rsjpark/A_Keyboard_For_Me/slide images/0.1_kle_to_matrix_converter.png

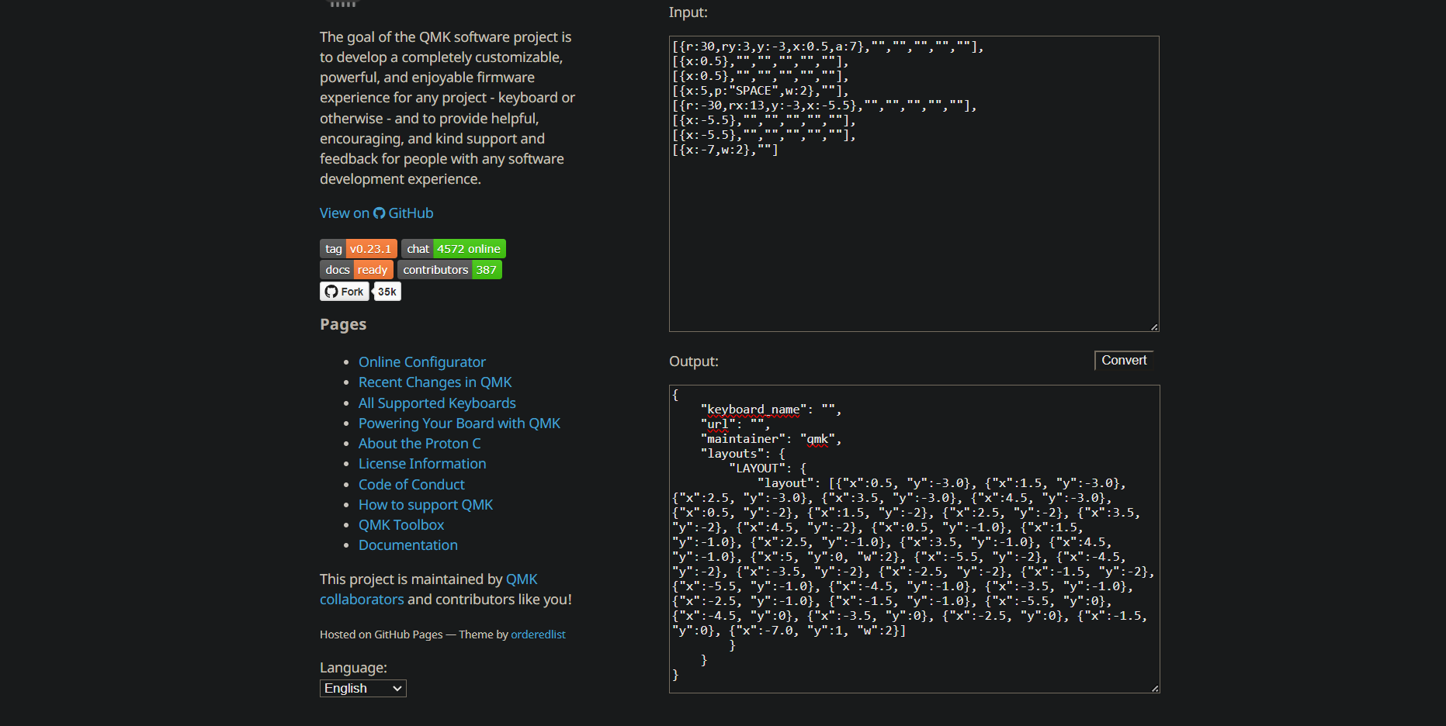
slide images/0.1_kle_to_matrix_converter.png
