rsjpark/A_Keyboard_For_Me/slide images/0.4_firmware_compile_trick.png

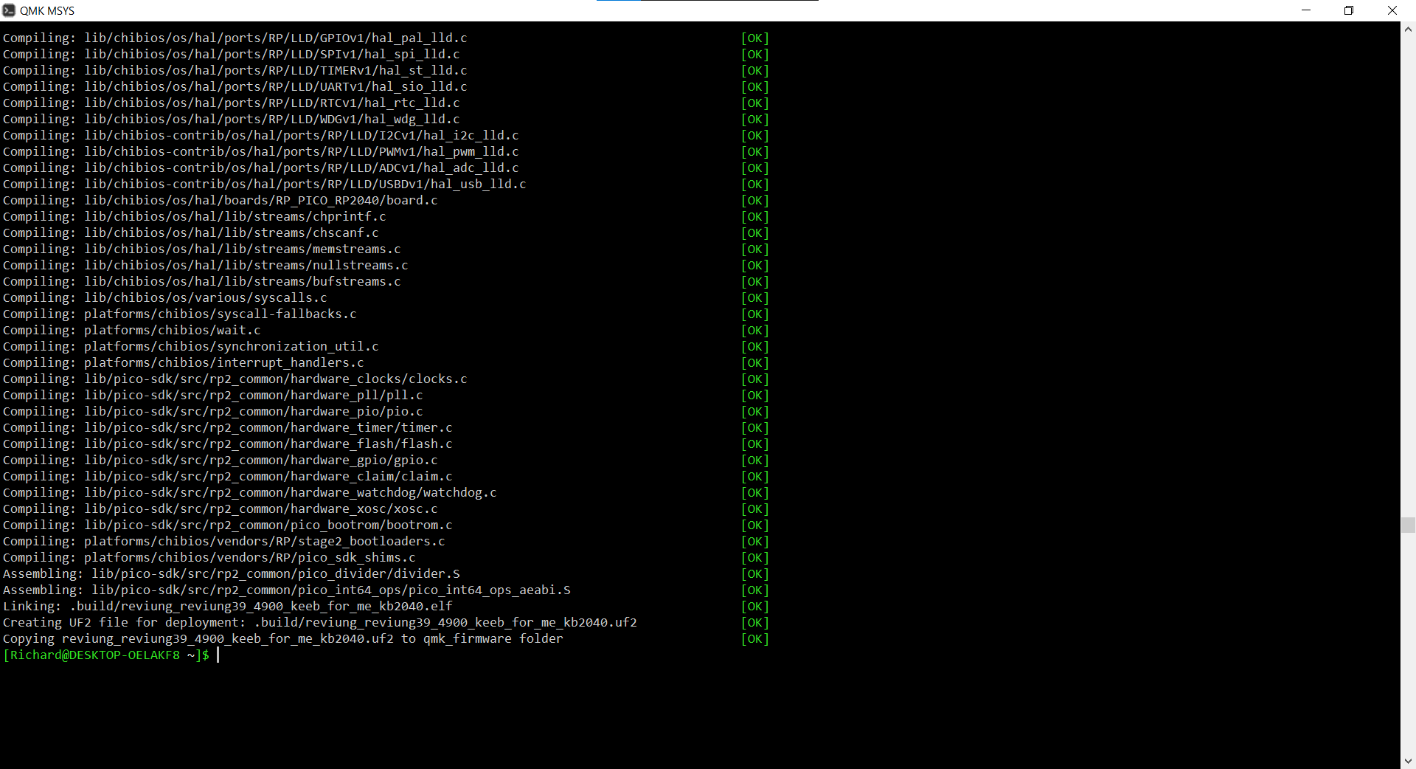
slide images/0.4_firmware_compile_trick.png
