rsjpark/A_Keyboard_For_Me/slide images/001.jpg

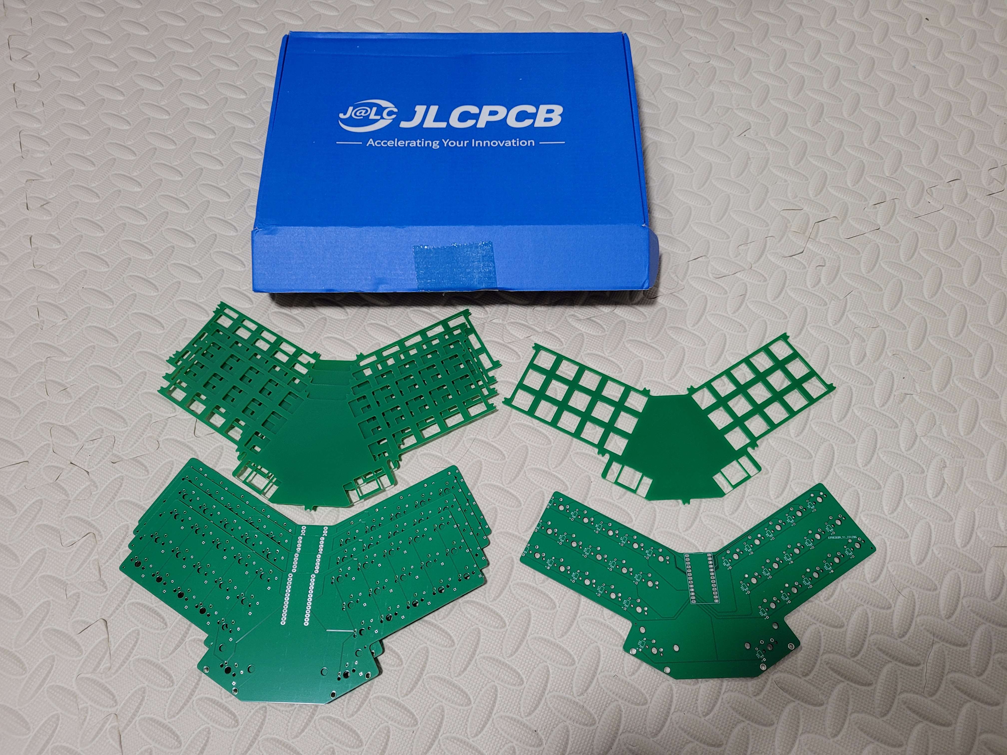
slide images/001.jpg
