rsjpark/A_Keyboard_For_Me/slide images/002.jpg

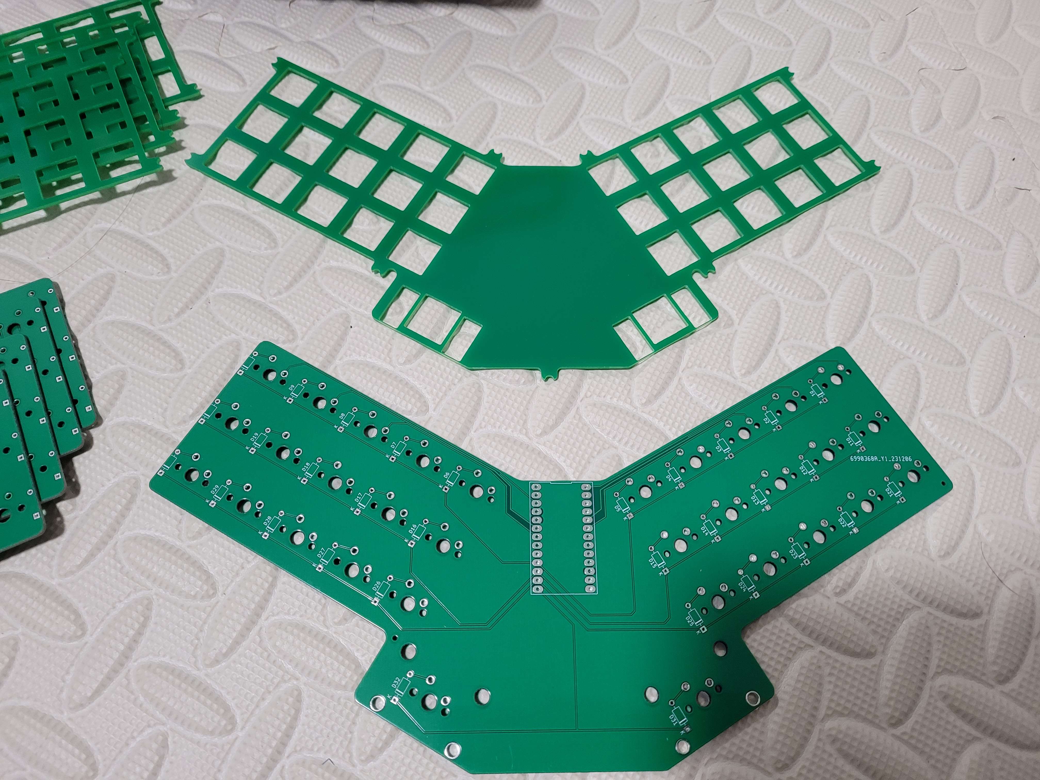
slide images/002.jpg
