rsjpark/A_Keyboard_For_Me/slide images/003.jpg

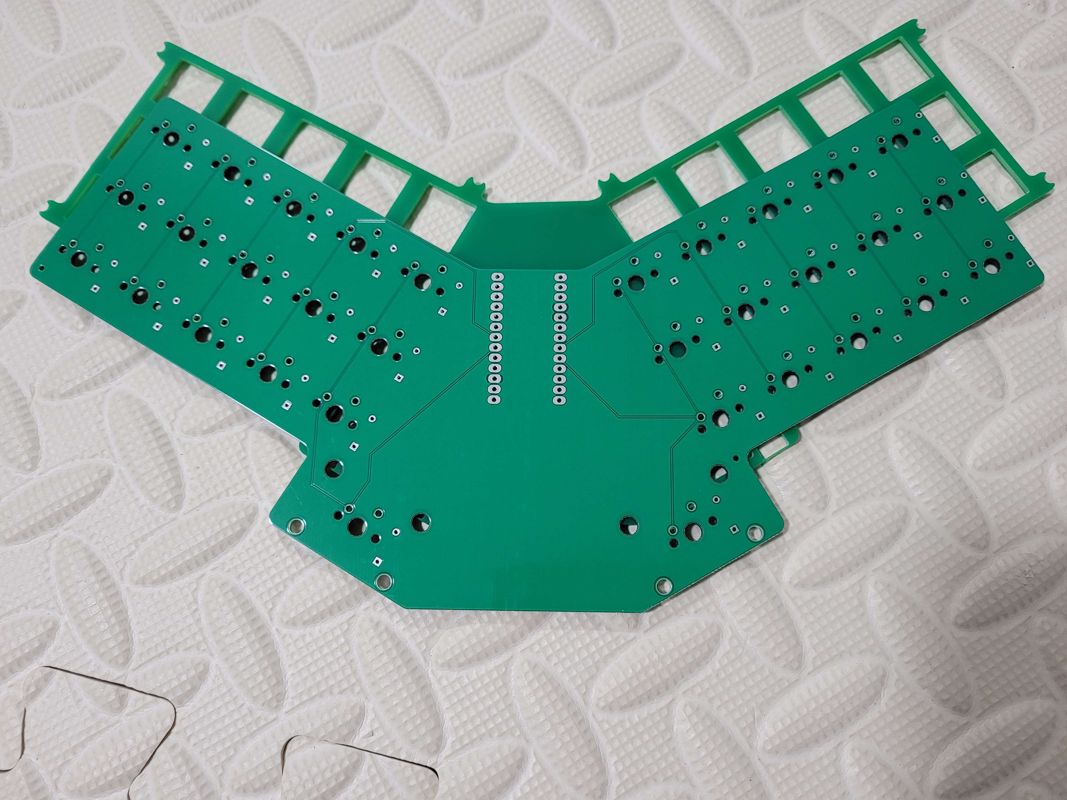
slide images/003.jpg
