rsjpark/A_Keyboard_For_Me/slide images/004.jpg

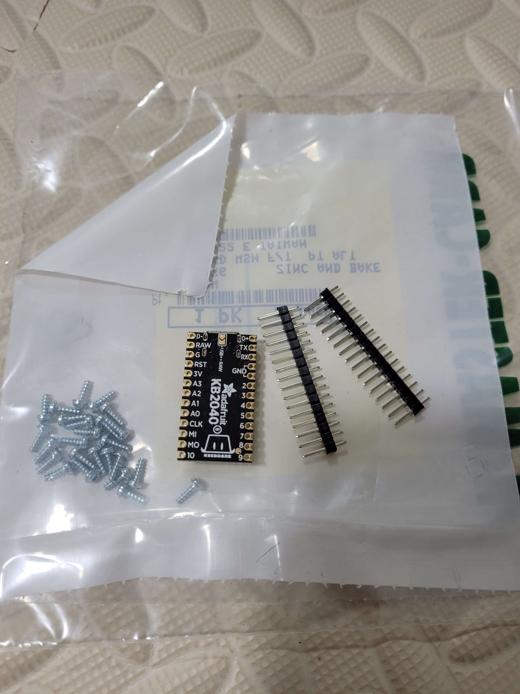
slide images/004.jpg
