rsjpark/A_Keyboard_For_Me/slide images/005.jpg

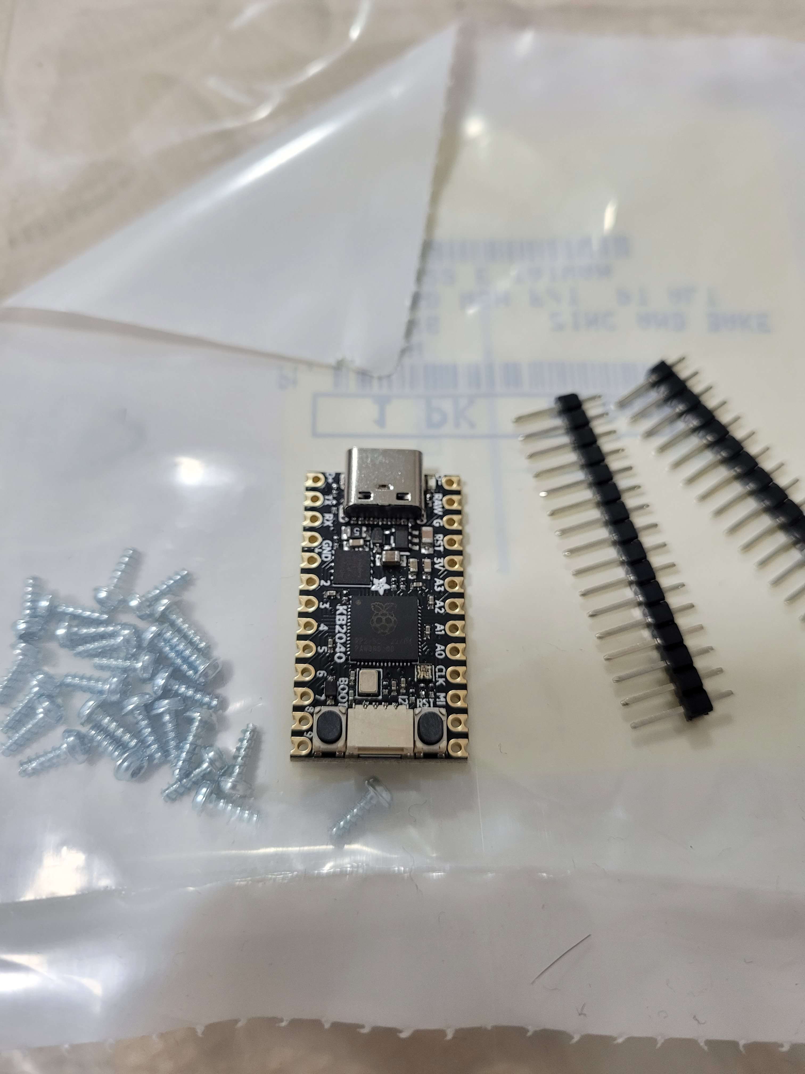
slide images/005.jpg
