rsjpark/A_Keyboard_For_Me/slide images/006.jpg

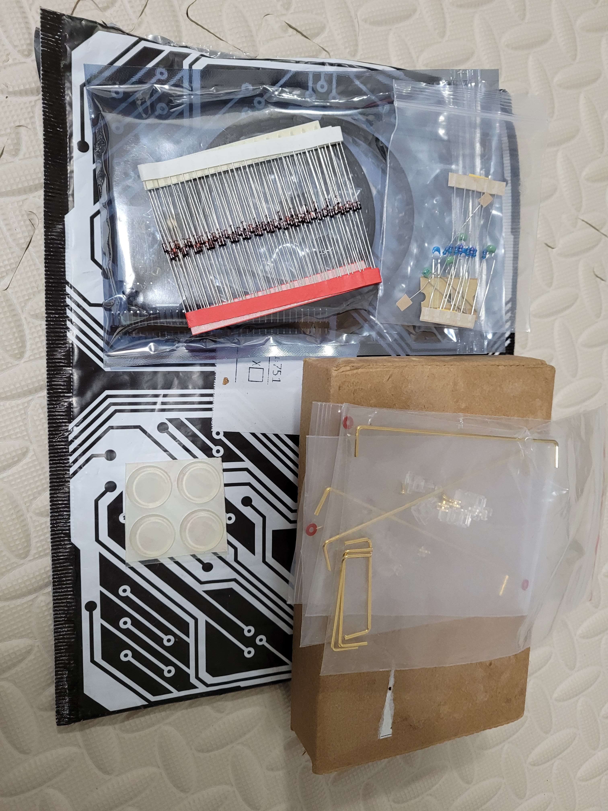
slide images/006.jpg
