rsjpark/A_Keyboard_For_Me/slide images/008.jpg

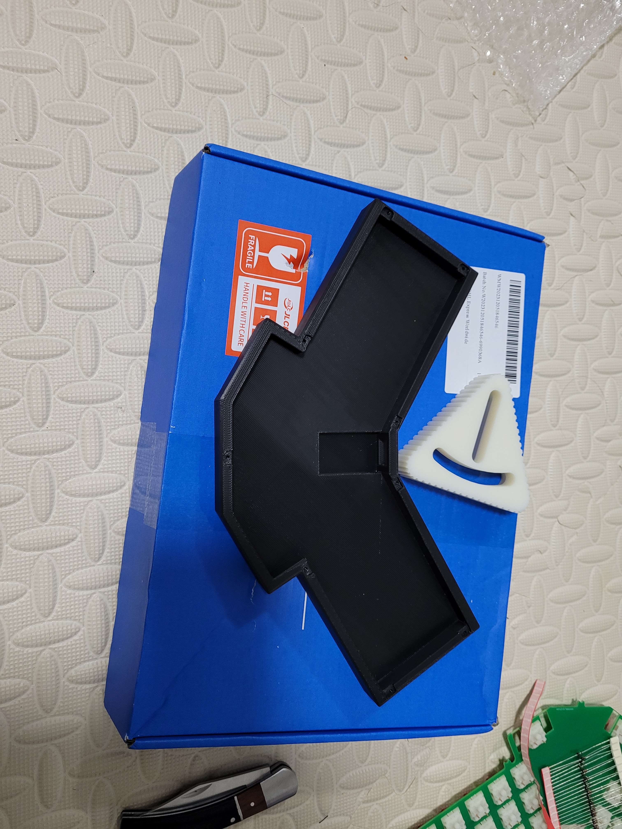
slide images/008.jpg
