rsjpark/A_Keyboard_For_Me/slide images/009.jpg

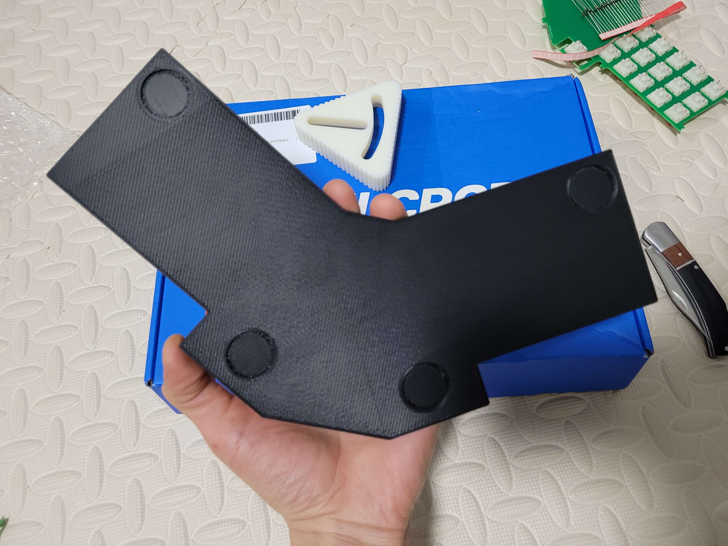
slide images/009.jpg
