rsjpark/A_Keyboard_For_Me/slide images/010.jpg

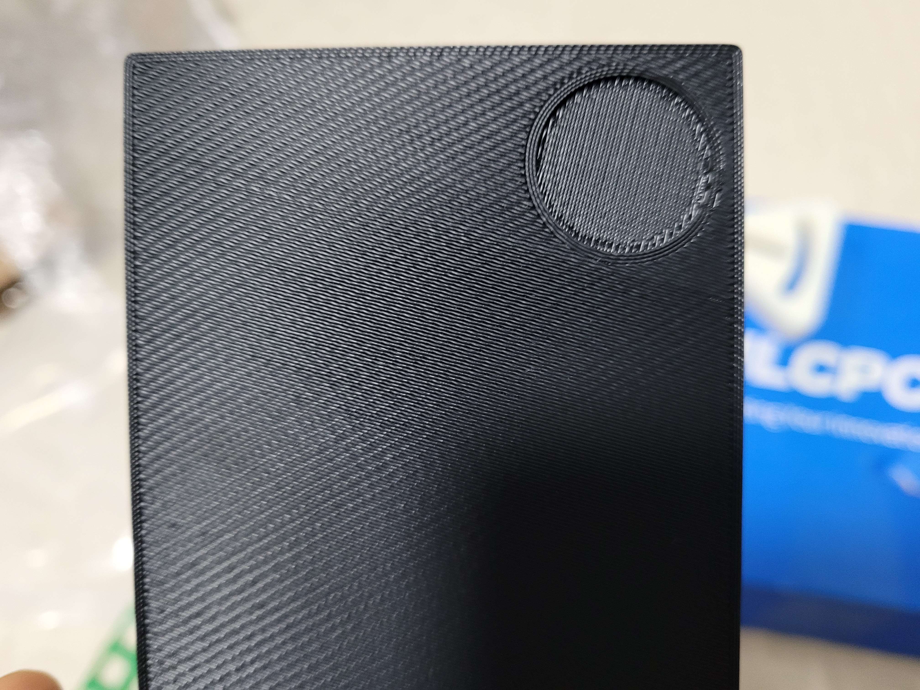
slide images/010.jpg
