rsjpark/A_Keyboard_For_Me/slide images/011.jpg

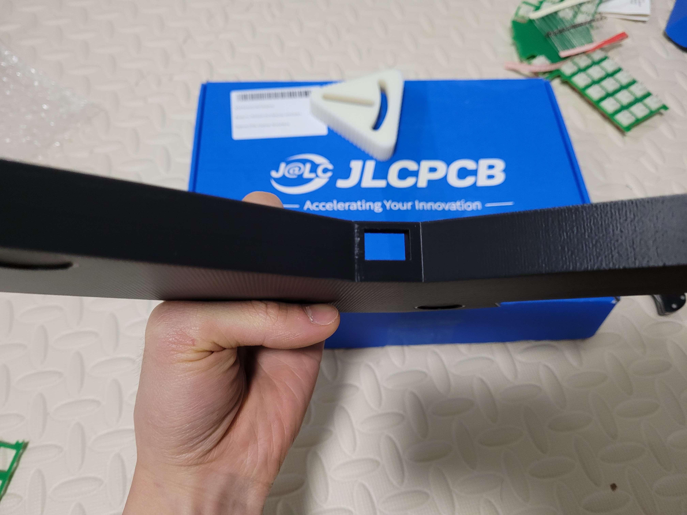
slide images/011.jpg
