rsjpark/A_Keyboard_For_Me/slide images/012.jpg

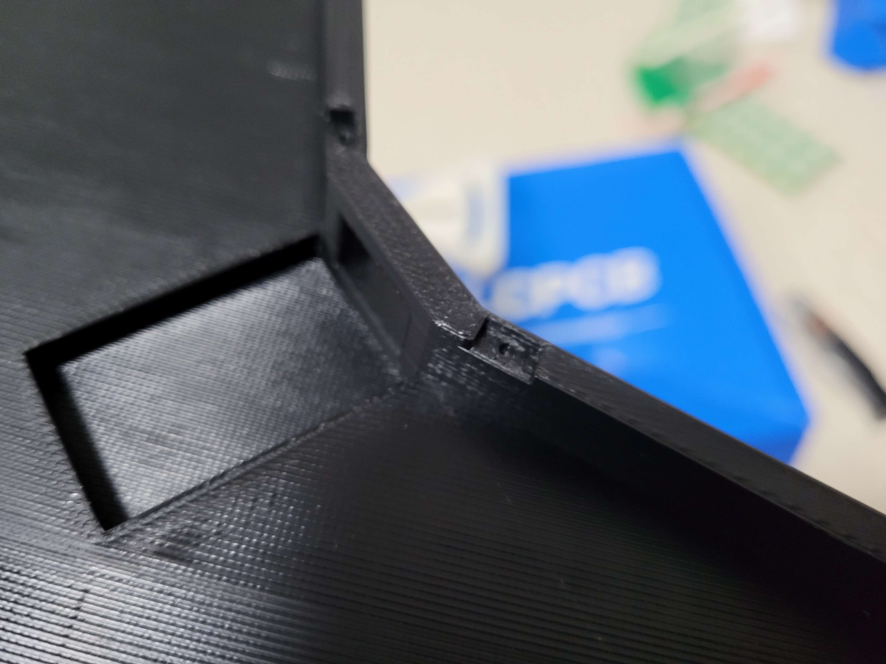
slide images/012.jpg
