rsjpark/A_Keyboard_For_Me/slide images/013.jpg

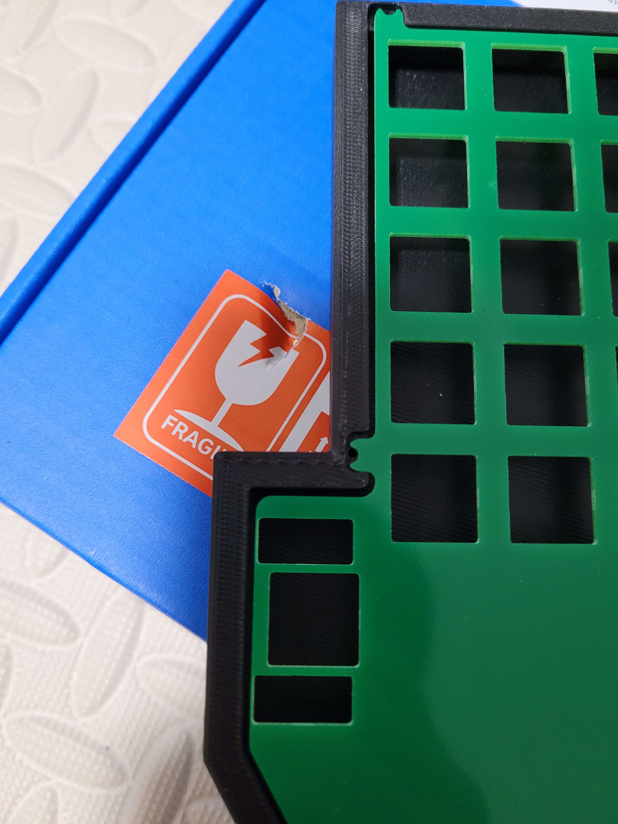
slide images/013.jpg
