rsjpark/A_Keyboard_For_Me/slide images/014.jpg

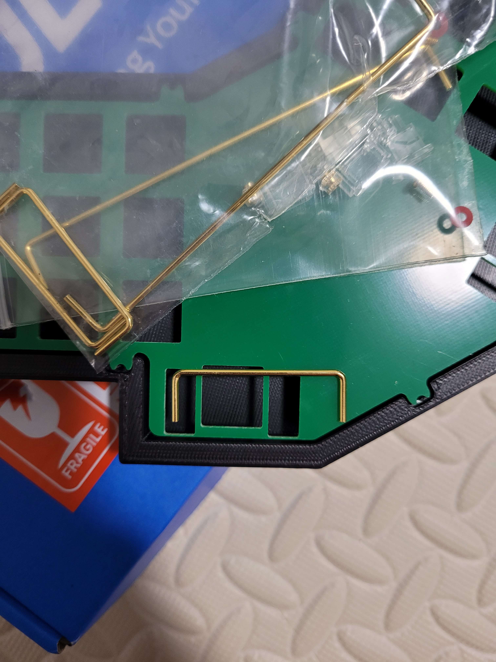
slide images/014.jpg
