rsjpark/A_Keyboard_For_Me/slide images/015.jpg

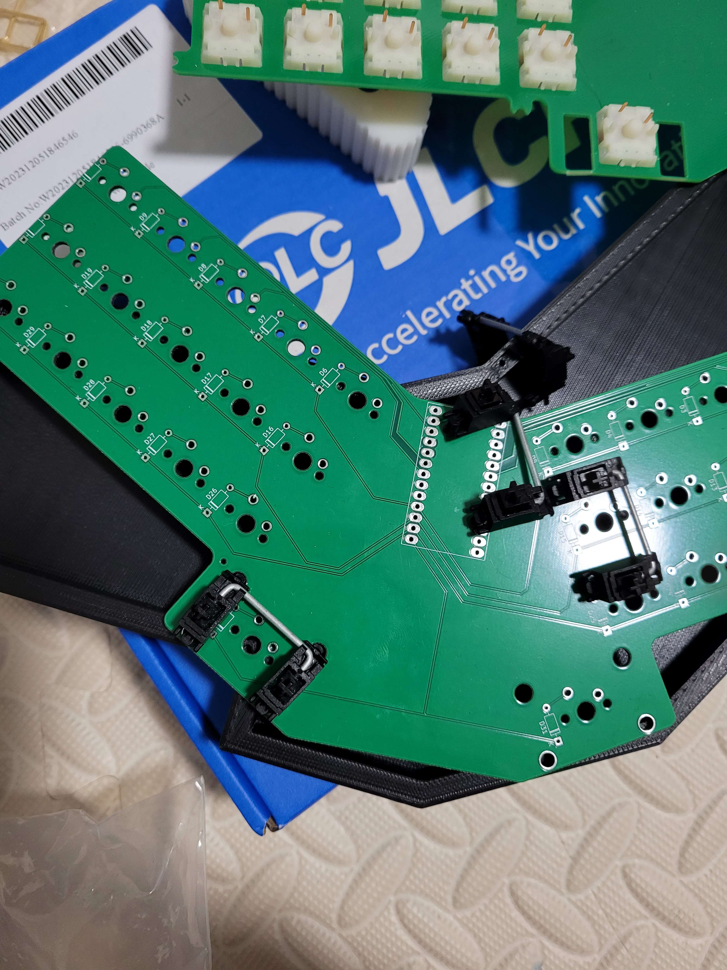
slide images/015.jpg
