rsjpark/A_Keyboard_For_Me/slide images/016.jpg

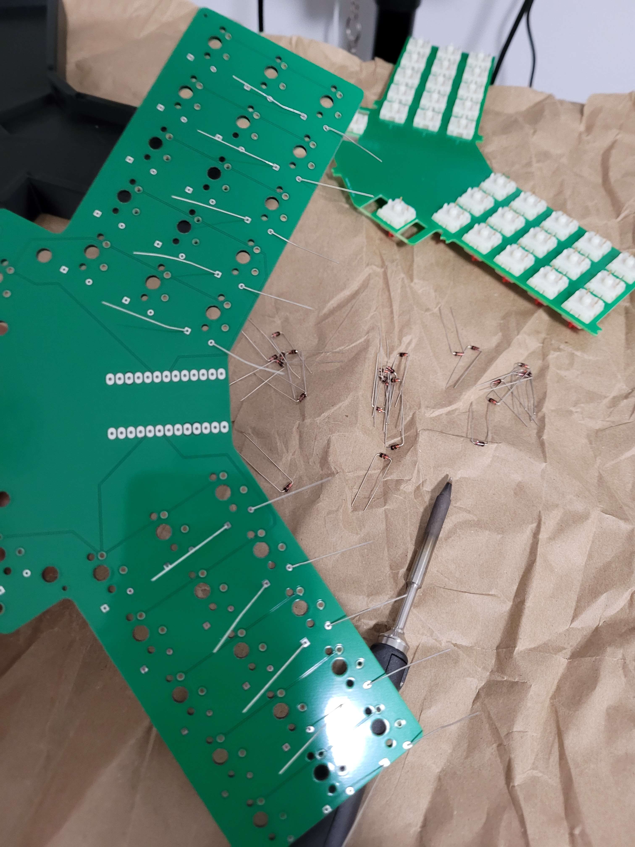
slide images/016.jpg
