rsjpark/A_Keyboard_For_Me/slide images/017.jpg

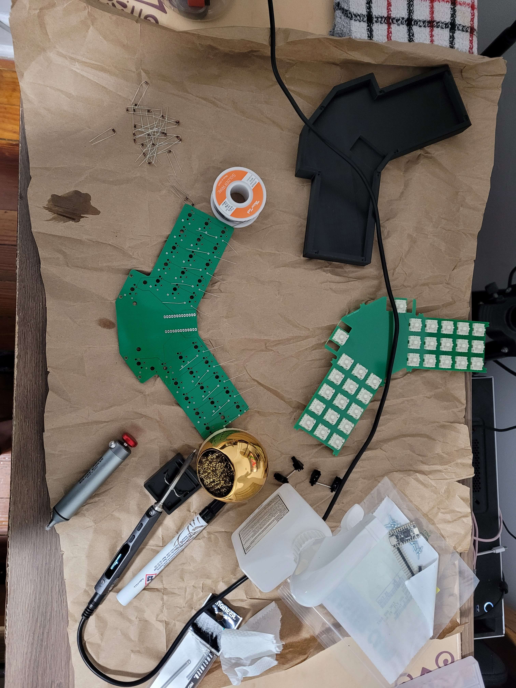
slide images/017.jpg
