rsjpark/A_Keyboard_For_Me/slide images/018.jpg

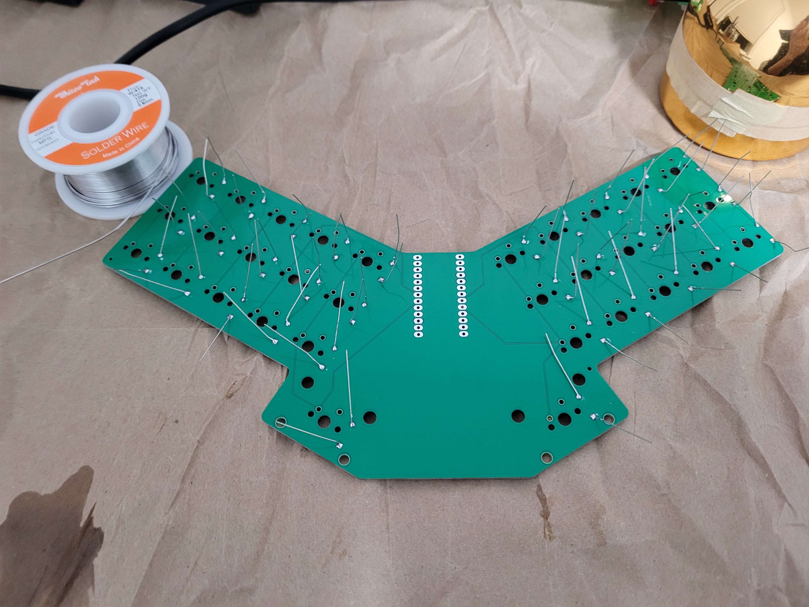
slide images/018.jpg
