rsjpark/A_Keyboard_For_Me/slide images/019.jpg

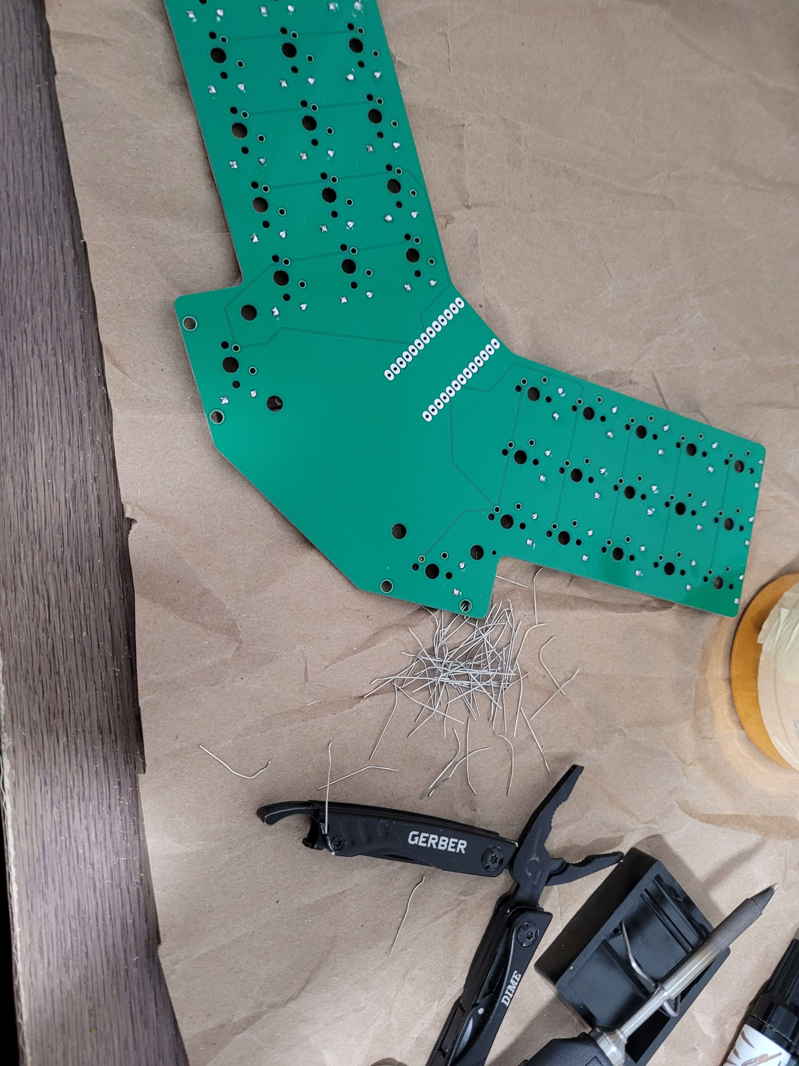
slide images/019.jpg
