rsjpark/A_Keyboard_For_Me/slide images/020.jpg

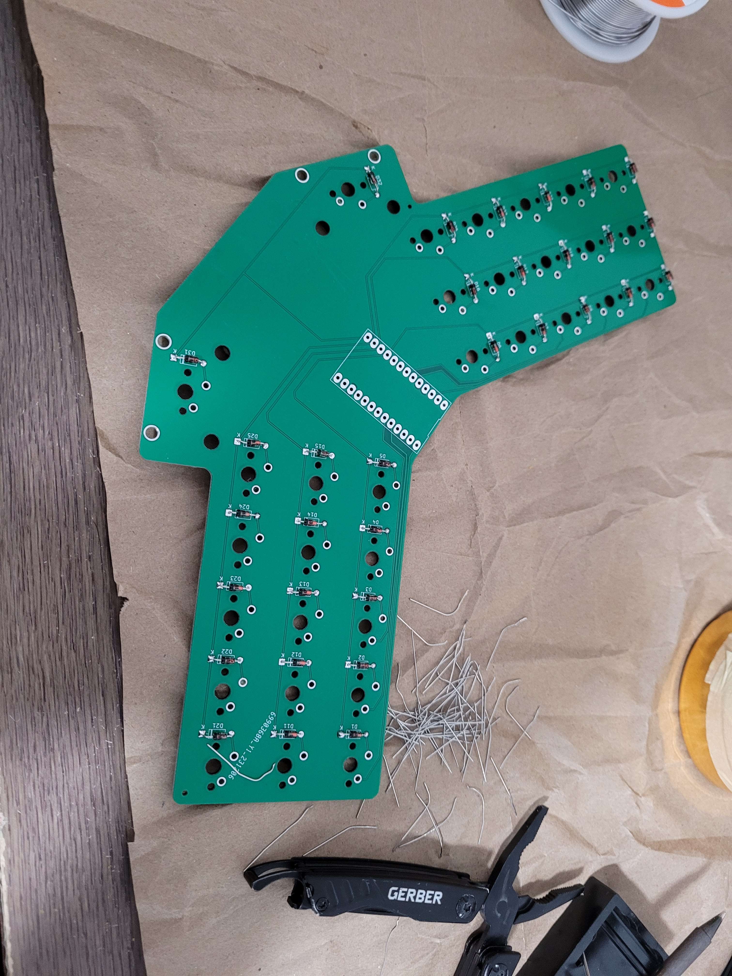
slide images/020.jpg
