rsjpark/A_Keyboard_For_Me/slide images/021.jpg

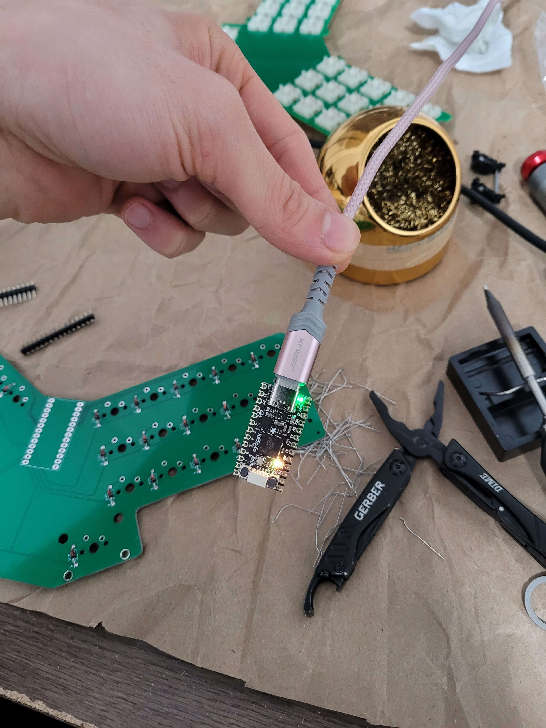
slide images/021.jpg
