rsjpark/A_Keyboard_For_Me/slide images/023.jpg

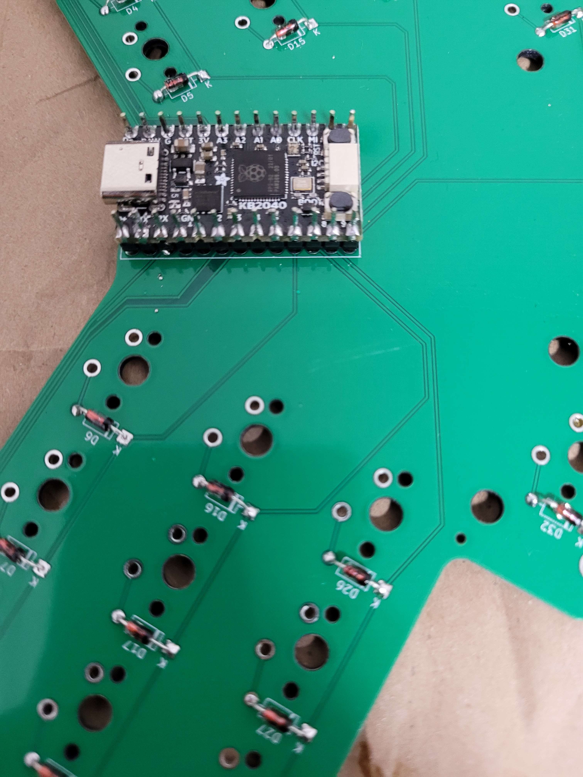
slide images/023.jpg
