rsjpark/A_Keyboard_For_Me/slide images/024.jpg

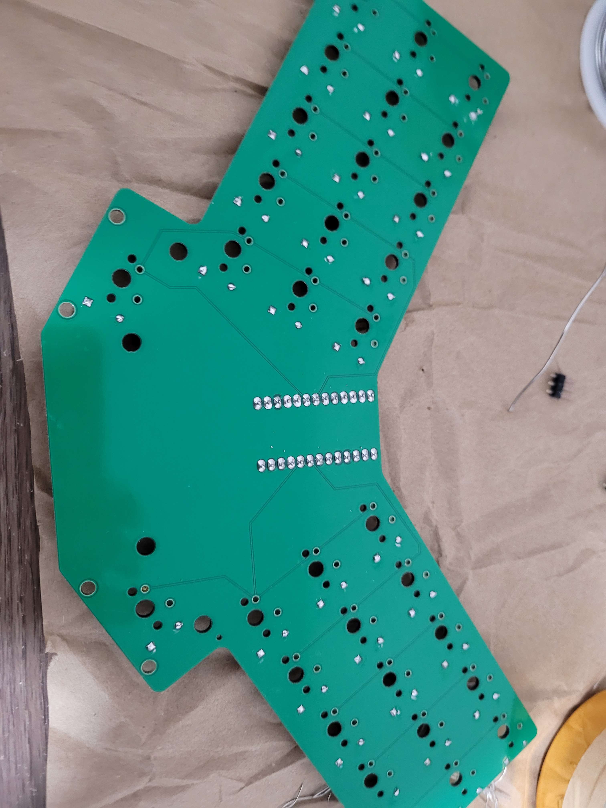
slide images/024.jpg
