rsjpark/A_Keyboard_For_Me/slide images/025.jpg

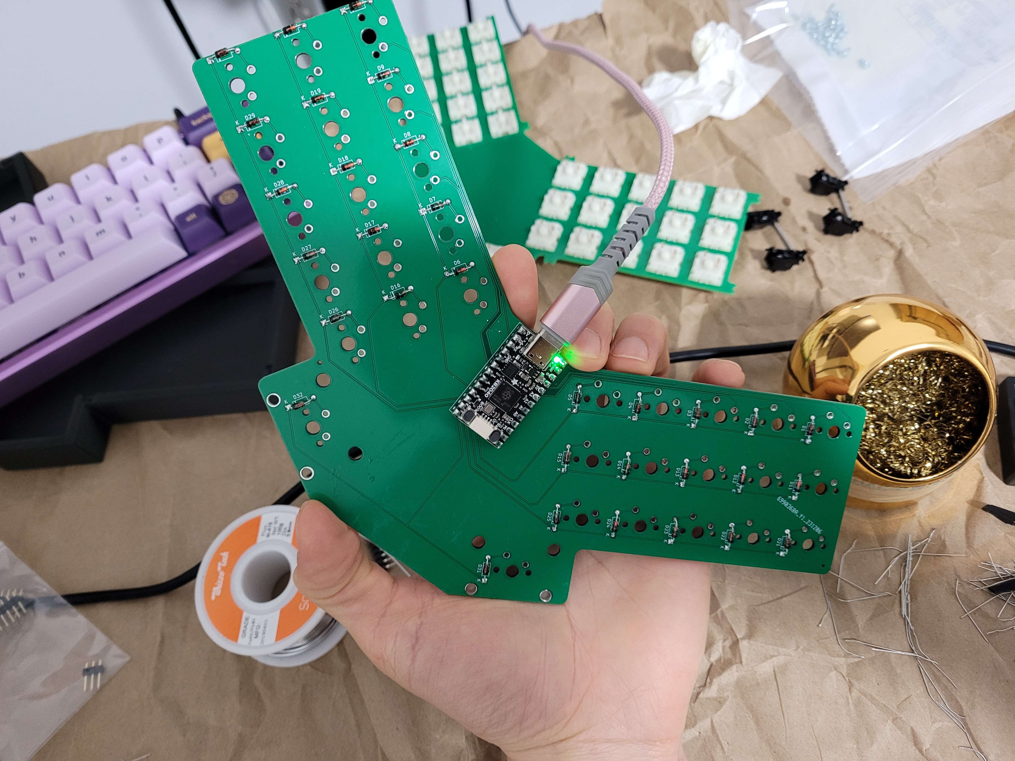
slide images/025.jpg
