rsjpark/A_Keyboard_For_Me/slide images/027.png

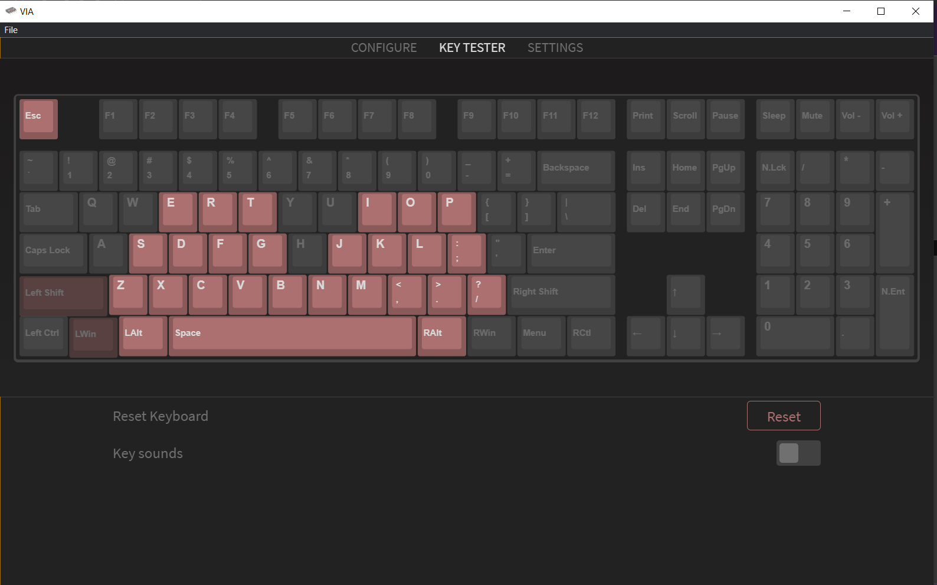
slide images/027.png
