rsjpark/A_Keyboard_For_Me/slide images/028.jpg

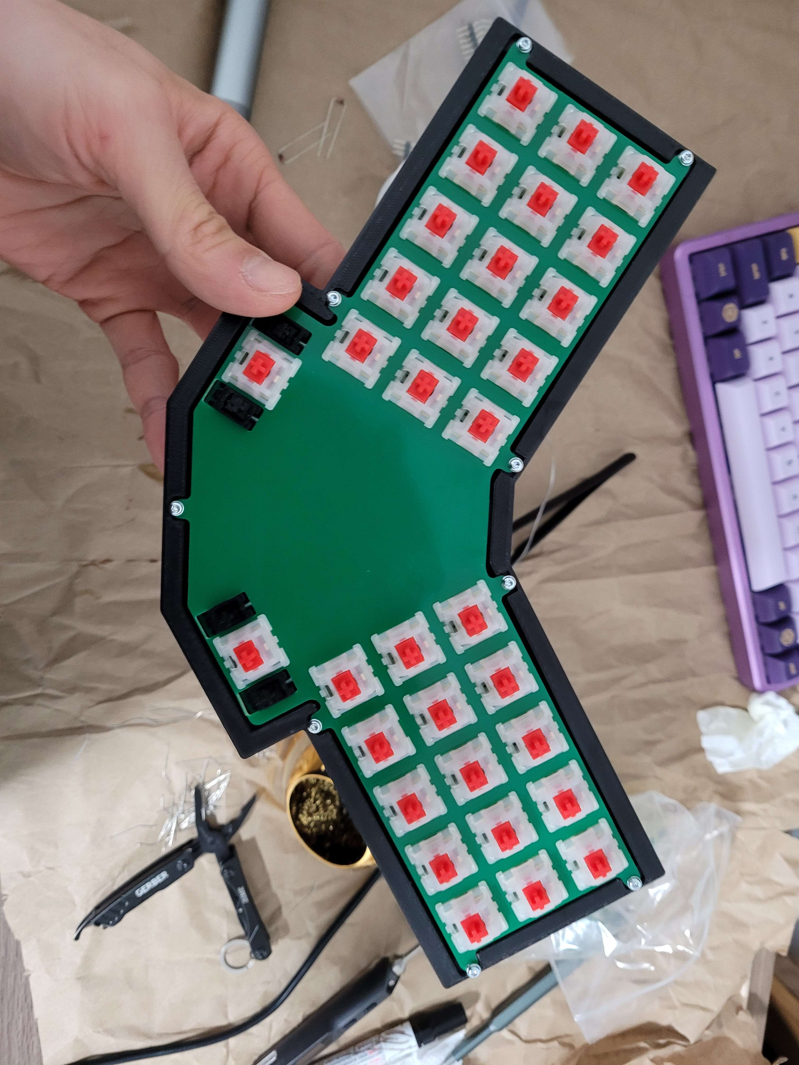
slide images/028.jpg
