rsjpark/A_Keyboard_For_Me/slide images/029.jpg

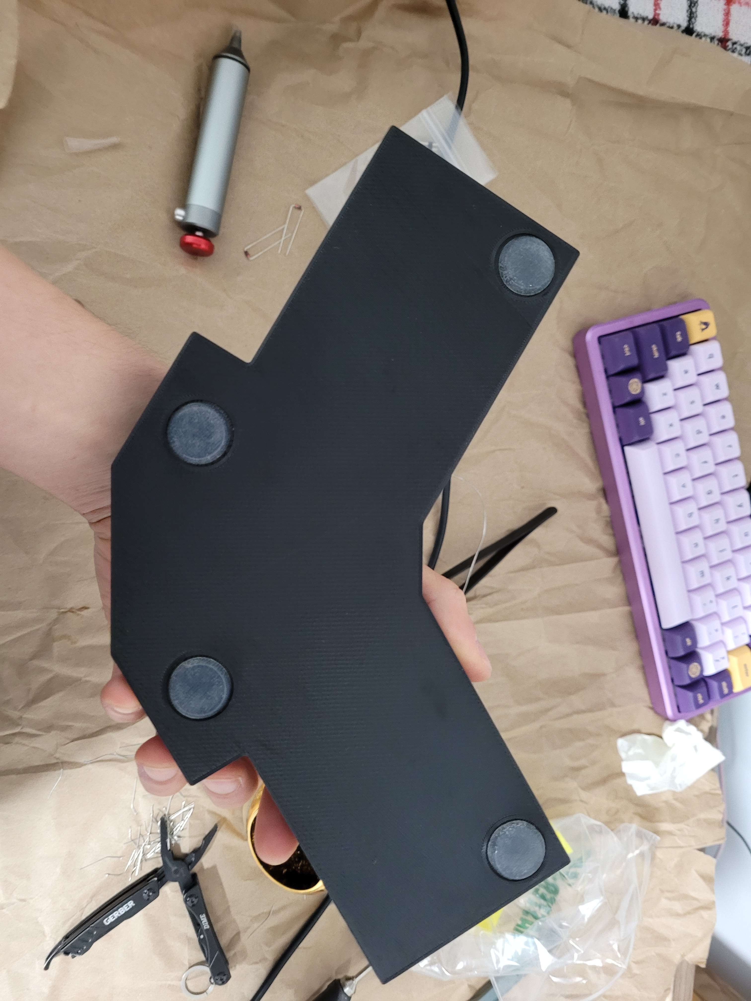
slide images/029.jpg
