rsjpark/A_Keyboard_For_Me/slide images/030.jpg

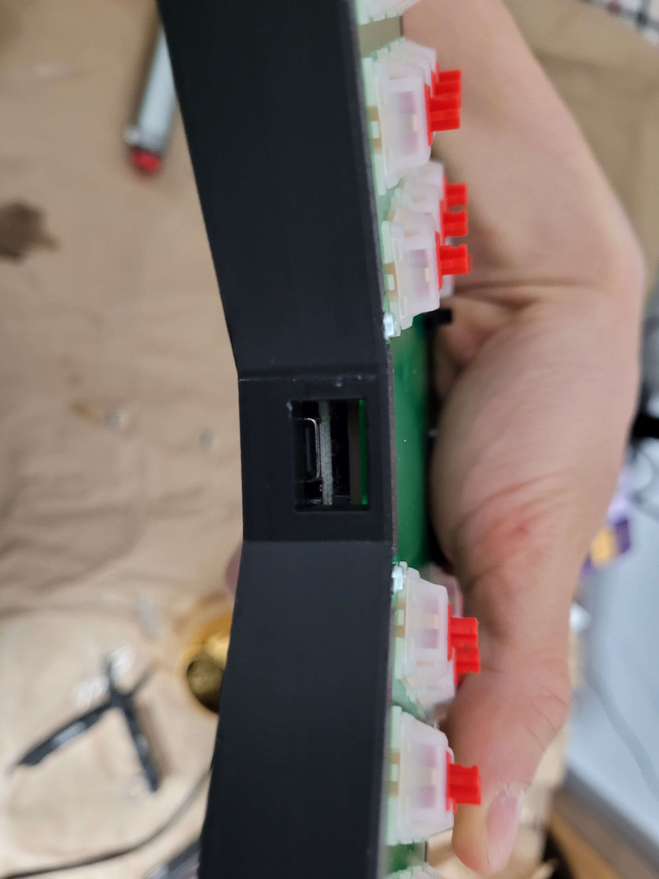
slide images/030.jpg
