rsjpark/A_Keyboard_For_Me/slide images/031.jpg

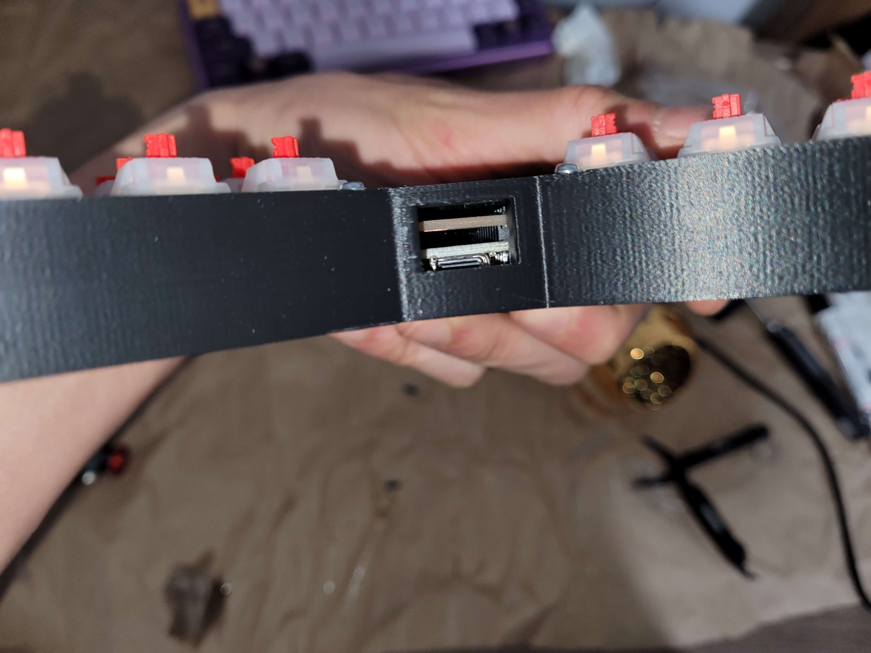
slide images/031.jpg
