rsjpark/A_Keyboard_For_Me/slide images/032.jpg

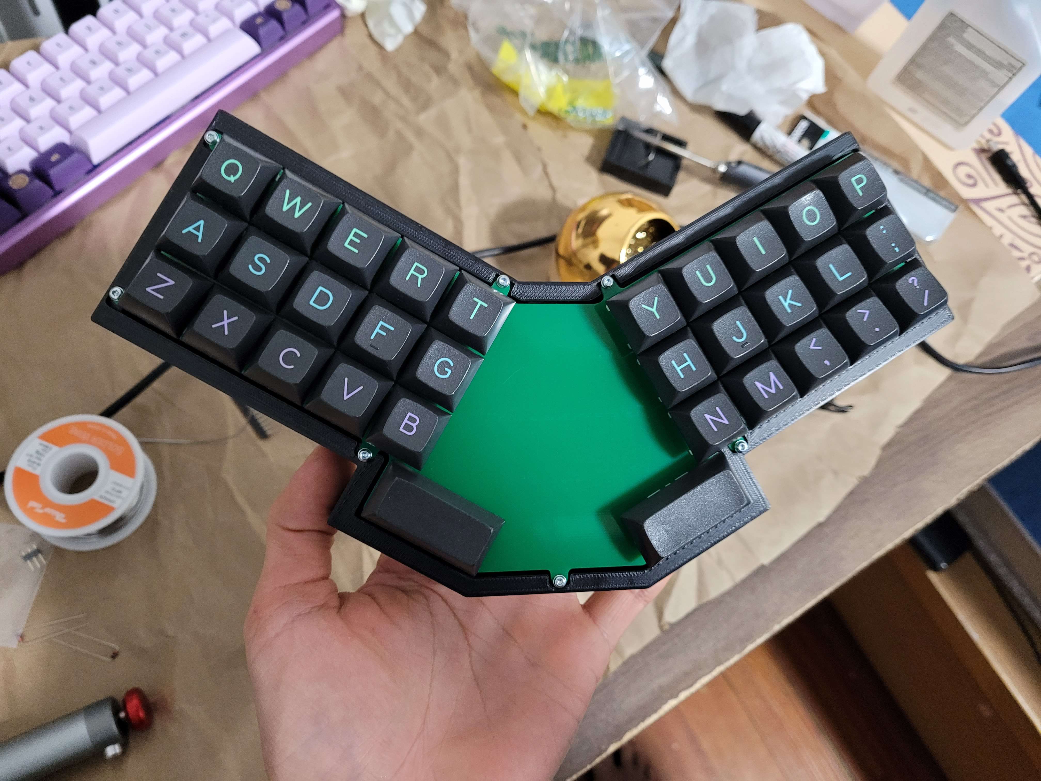
slide images/032.jpg
