rsjpark/A_Keyboard_For_Me/slide images/033.jpg

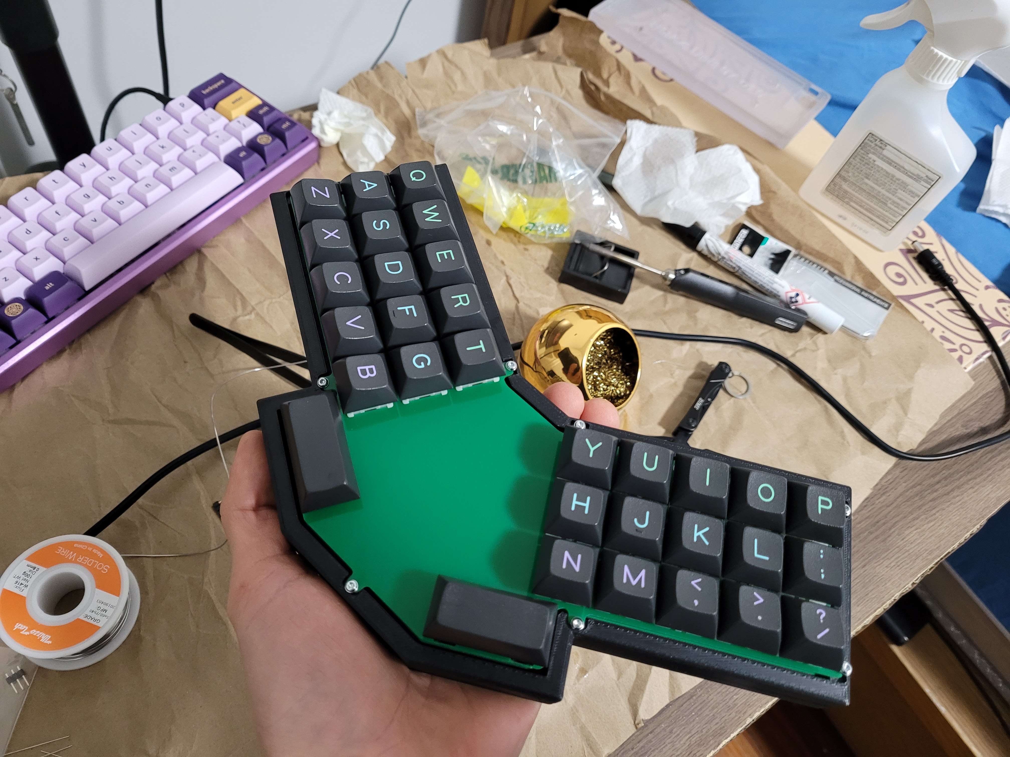
slide images/033.jpg
