rsjpark/A_Keyboard_For_Me/slide images/034.jpg

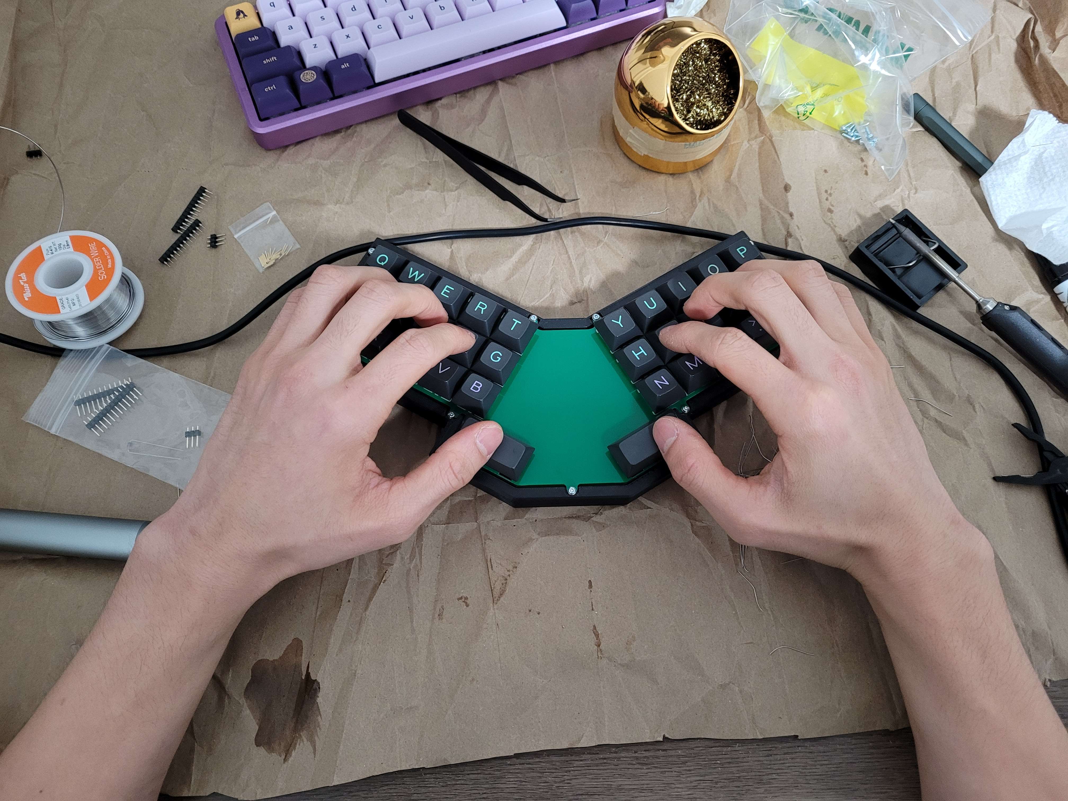
slide images/034.jpg
