rsjpark/A_Keyboard_For_Me/slide images/035.jpg

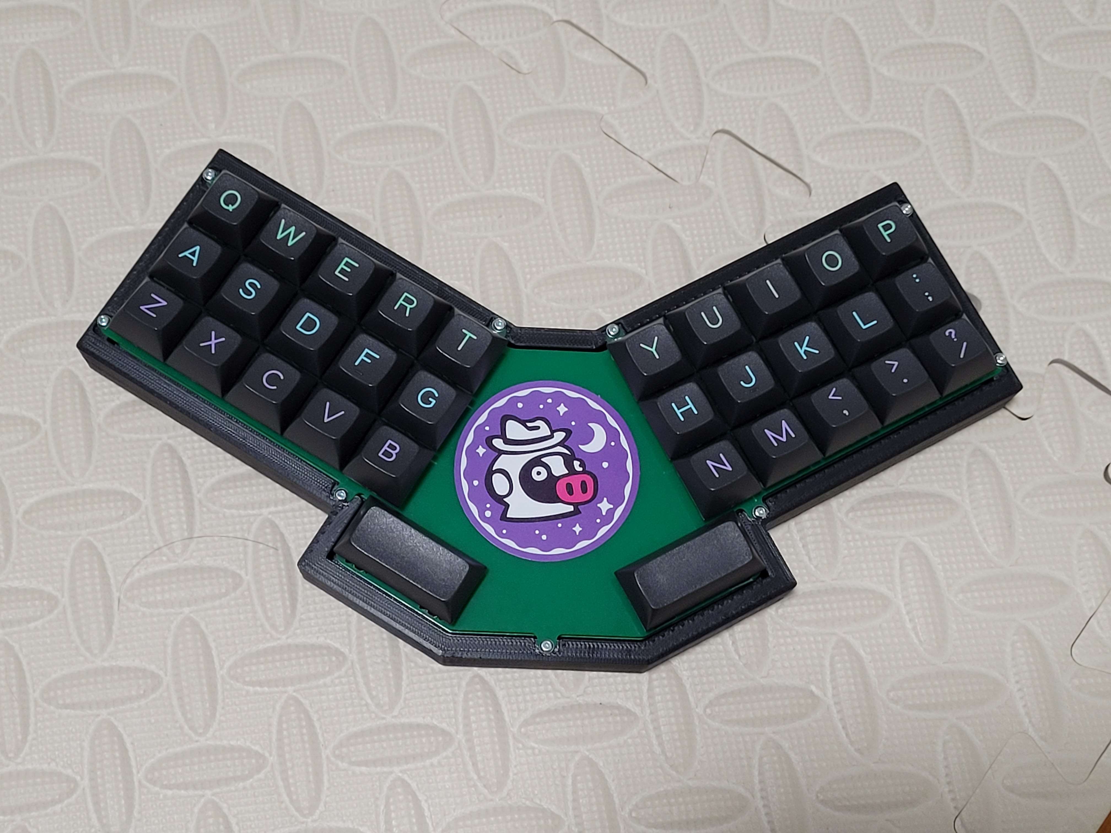
slide images/035.jpg
