rsjpark/A_Keyboard_For_Me/slide images/.002_pcb_schem_bad.png

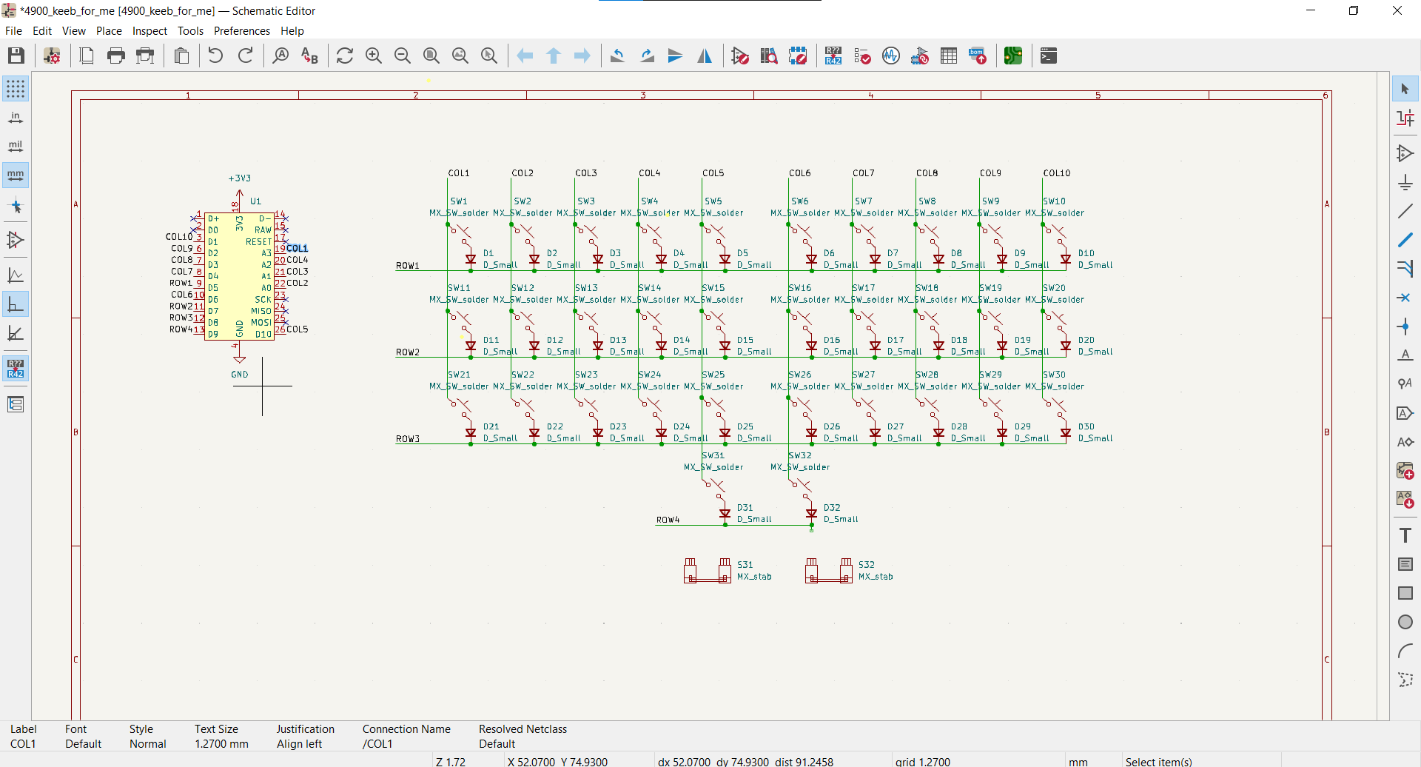
slide images/.002_pcb_schem_bad.png
