rsjpark/A_Keyboard_For_Me/slide images/.003_pcb_pcb_bad.png

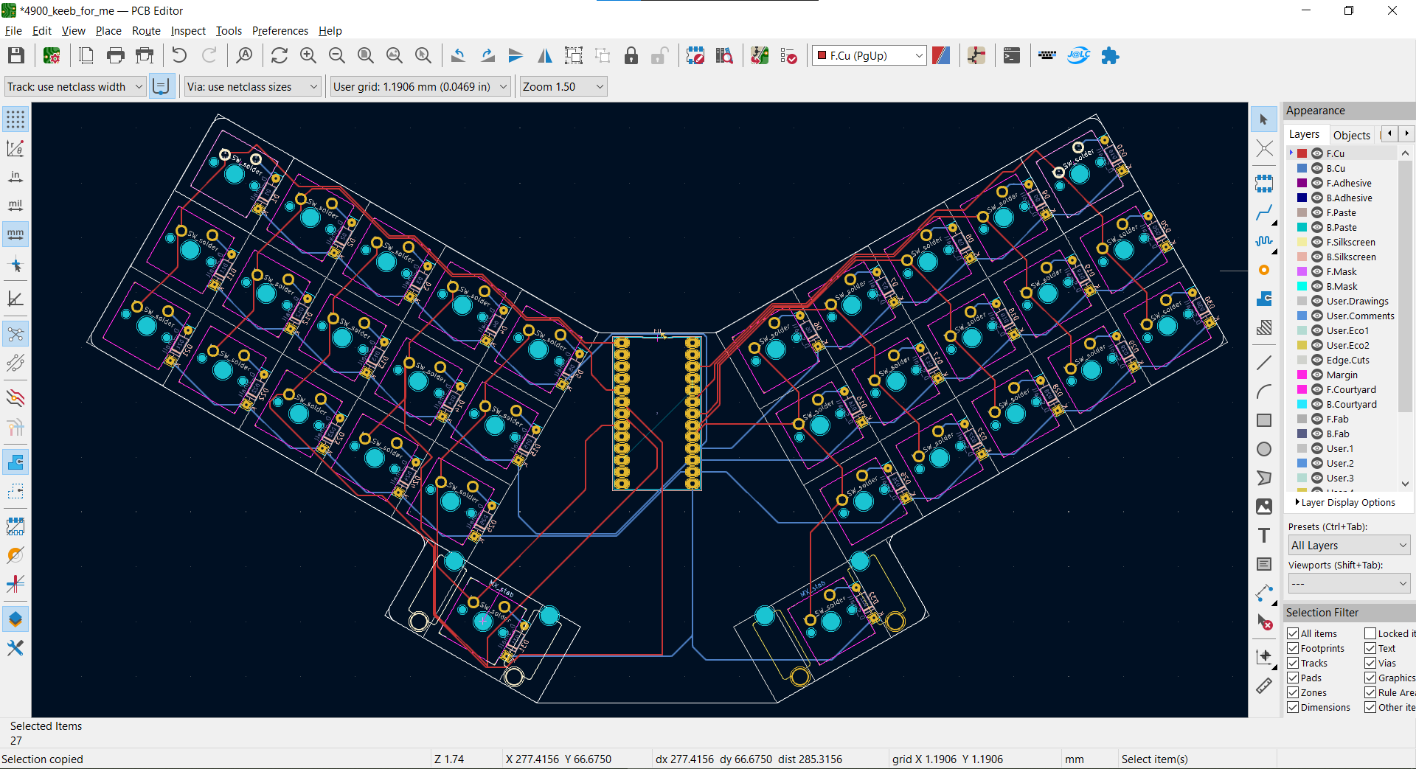
slide images/.003_pcb_pcb_bad.png
